Aces-Electronics/ae-temperature-monitor/firmware/src/services/ble_service.cpp

#include "ble_service.h"
#include <Arduino.h>
#include <WiFi.h>

// UUIDs
#define SERVICE_UUID        "4fafc201-1fb5-459e-8fcc-c5c9c331914b" // Reuse Smart Shunt Service for now or defined new
#define TEMP_CHAR_UUID      "beb5483e-36e1-4688-b7f5-ea07361b26a9" // Similar to Voltage but last digit 9
#define SLEEP_CHAR_UUID     "3A1B2C3D-4E5F-6A7B-8C9D-0E1F2A3B4C60" // Reuse disconnect delay or new?
// Actually let's use a specific one for Temp Sensor to distinguish?
// User said: "profiles for the BLE app so that it knows which device is connected"
// I will use a different Service UUID or just different characteristics.
// Let's stick to the Smart Shunt Service UUID for simplicity in discovery but specific characteristics.

#define TEMP_SENSOR_SERVICE_UUID "181A" // Environmental Sensing Service (Standard) or Custom?
// Let's use Custom to match user pattern.
#define AE_TEMP_SERVICE_UUID "4fafc201-1fb5-459e-8fcc-c5c9c331914c" // Ended with 'c'

#define CHAR_TEMP_UUID       "beb5483e-36e1-4688-b7f5-ea07361b26aa"
#define CHAR_SLEEP_UUID      "beb5483e-36e1-4688-b7f5-ea07361b26ab"
#define CHAR_BATT_UUID       "beb5483e-36e1-4688-b7f5-ea07361b26ac"
#define CHAR_NAME_UUID       "beb5483e-36e1-4688-b7f5-ea07361b26ad"
#define CHAR_PAIRED_UUID     "beb5483e-36e1-4688-b7f5-ea07361b26ae"
#define WIFI_SSID_CHAR_UUID  "5A1B2C3D-4E5F-6A7B-8C9D-0E1F2A3B4C62"
#define WIFI_PASS_CHAR_UUID  "6A1B2C3D-4E5F-6A7B-8C9D-0E1F2A3B4C63"

BleService bleService;

class ServerCallbacks: public NimBLEServerCallbacks {
    void onConnect(NimBLEServer* pServer) {
        Serial.println("Client connected");
    };
    void onDisconnect(NimBLEServer* pServer) {
        Serial.println("Client disconnected");
    }
};

class PairedCallback: public NimBLECharacteristicCallbacks {
    void onWrite(NimBLECharacteristic* pCharacteristic) {
        std::string value = pCharacteristic->getValue();
        if (value.length() > 0) {
            String valStr = String(value.c_str());
            Serial.printf("[BLE WRITE] Paired/Reset Command: %s\n", valStr.c_str());
            
            if (valStr.startsWith("{")) {
                // JSON Payload -> Pairing Data
                if (bleService._pairingDataCallback) {
                     bleService._pairingDataCallback(valStr.c_str());
                }
            } else if (valStr == "FORCE_OTA") {
                 Serial.println("[BLE] FORCE_OTA command received.");
                 if (bleService._forceOtaCallback) {
                      bleService._forceOtaCallback();
                 }
            } else if (valStr == "RESET" || valStr == "UNPAIR") {
                // Reset Command
                 Serial.println("Received RESET command");
                 bleService.updatePaired(false);
            } 
        }
    }
};

class WifiSsidCallback: public NimBLECharacteristicCallbacks {
    void onWrite(NimBLECharacteristic* pCharacteristic) {
        std::string value = pCharacteristic->getValue();
        if (value.length() > 0) {
             bleService._tempSsid = String(value.c_str());
             Serial.printf("[BLE WRITE] WiFi SSID: %s\n", bleService._tempSsid.c_str());
             // Pass partial or full data. If Pass is already set, this might be a refresh.
             if (bleService._wifiCallback) {
                  bleService._wifiCallback(bleService._tempSsid.c_str(), bleService._tempPass.c_str());
             }
        }
    }
};

class WifiPassCallback: public NimBLECharacteristicCallbacks {
    void onWrite(NimBLECharacteristic* pCharacteristic) {
        std::string value = pCharacteristic->getValue();
        if (value.length() > 0) {
             bleService._tempPass = String(value.c_str());
             Serial.println("[BLE WRITE] WiFi Pass received");
             if (bleService._wifiCallback) {
                  bleService._wifiCallback(bleService._tempSsid.c_str(), bleService._tempPass.c_str());
             }
        }
    }
};

class SleepCallback: public NimBLECharacteristicCallbacks {
    void onWrite(NimBLECharacteristic* pCharacteristic) {
        std::string value = pCharacteristic->getValue();
        if (value.length() == 4) {
             uint32_t interval = *(uint32_t*)value.data();
             bleService.setSleepInterval(interval);
             Serial.printf("[BLE WRITE] Sleep Interval: %d ms\n", interval);
        }
    }
};

class NameCallback: public NimBLECharacteristicCallbacks {
    void onWrite(NimBLECharacteristic* pCharacteristic) {
        std::string value = pCharacteristic->getValue();
        if (value.length() > 0) {
             Serial.printf("[BLE WRITE] Device Name: %s\n", value.c_str());
             bleService.updateName(value.c_str()); // Helper to notify listener
        }
    }
};


// Helper to generate PIN from MAC (Matches Shunt)
uint32_t generatePinFromMac() {
    uint8_t mac[6];
    WiFi.macAddress(mac);
    // Use last 3 bytes to generate a unique 6-digit PIN
    uint32_t val = (mac[3] << 16) | (mac[4] << 8) | mac[5];
    uint32_t pin = val % 1000000;
    Serial.printf("[BLE SEC] PIN Code: %06d\n", pin);
    return pin;
}

void BleService::begin(const char* deviceName) {
    NimBLEDevice::init(deviceName);
    NimBLEDevice::setPower(ESP_PWR_LVL_P9);
    
    // Security & Speed Configuration (Matches Shunt)
    uint32_t passkey = generatePinFromMac();
    NimBLEDevice::setSecurityAuth(true, true, true); // Bonding, MITM, Secure Connection
    NimBLEDevice::setSecurityPasskey(passkey);
    NimBLEDevice::setSecurityIOCap(BLE_HS_IO_DISPLAY_ONLY); // Forces user to enter PIN on phone
    
    _pServer = NimBLEDevice::createServer();
    _pServer->setCallbacks(new ServerCallbacks());
    
    _pService = _pServer->createService(AE_TEMP_SERVICE_UUID);
    
    _pTempChar = _pService->createCharacteristic(
        CHAR_TEMP_UUID,
        NIMBLE_PROPERTY::READ | NIMBLE_PROPERTY::NOTIFY | NIMBLE_PROPERTY::READ_ENC
    );
    
    _pSleepChar = _pService->createCharacteristic(
        CHAR_SLEEP_UUID,
        NIMBLE_PROPERTY::READ | NIMBLE_PROPERTY::WRITE | NIMBLE_PROPERTY::READ_ENC | NIMBLE_PROPERTY::WRITE_ENC
    );
    _pSleepChar->setCallbacks(new SleepCallback());
    _pSleepChar->setValue((uint8_t*)&_sleepIntervalMs, 4);
    
    _pBattChar = _pService->createCharacteristic(
        CHAR_BATT_UUID,
        NIMBLE_PROPERTY::READ | NIMBLE_PROPERTY::NOTIFY | NIMBLE_PROPERTY::READ_ENC
    );
    
    
    _pNameChar = _pService->createCharacteristic(
        CHAR_NAME_UUID,
        NIMBLE_PROPERTY::READ | NIMBLE_PROPERTY::WRITE | NIMBLE_PROPERTY::NOTIFY | NIMBLE_PROPERTY::READ_ENC | NIMBLE_PROPERTY::WRITE_ENC
    );
    _pNameChar->setCallbacks(new NameCallback());
    _pNameChar->setValue(deviceName);

    // PAIRED Characteristic
    _pPairedChar = _pService->createCharacteristic(
        CHAR_PAIRED_UUID,
        NIMBLE_PROPERTY::READ | NIMBLE_PROPERTY::WRITE | NIMBLE_PROPERTY::NOTIFY | NIMBLE_PROPERTY::READ_ENC | NIMBLE_PROPERTY::WRITE_ENC
    );
    // Set initial value to WiFi MAC Address
    String mac = WiFi.macAddress();
    _pPairedChar->setValue(mac.c_str());
    _pPairedChar->setCallbacks(new PairedCallback());

    // WIFI Credentials
    _pWifiSsidChar = _pService->createCharacteristic(
        WIFI_SSID_CHAR_UUID,
         NIMBLE_PROPERTY::WRITE | NIMBLE_PROPERTY::WRITE_ENC
    );
    _pWifiSsidChar->setCallbacks(new WifiSsidCallback());
    
    _pWifiPassChar = _pService->createCharacteristic(
        WIFI_PASS_CHAR_UUID,
         NIMBLE_PROPERTY::WRITE | NIMBLE_PROPERTY::WRITE_ENC
    );
    _pWifiPassChar->setCallbacks(new WifiPassCallback());

    // Start Service
    _pService->start();

    // Start Advertising
    NimBLEAdvertising* pAdvertising = NimBLEDevice::getAdvertising();
    pAdvertising->addServiceUUID(AE_TEMP_SERVICE_UUID); // Advertise Service UUID
    // Explicitly add Name to Scan Response to handle long suffixes
    NimBLEAdvertisementData oScanResponseData = NimBLEAdvertisementData();
    oScanResponseData.setName(deviceName);
    pAdvertising->setScanResponseData(oScanResponseData);
    
    pAdvertising->setScanResponse(true);
    pAdvertising->start();
    
    Serial.println("BLE Started (Secure)");
}

void BleService::updateTemperature(float temp) {
    if (_pTempChar) {
        _pTempChar->setValue(temp);
        _pTempChar->notify();
    }
}

void BleService::updateBatteryLevel(int level) {
    if (_pBattChar) {
        _pBattChar->setValue((uint32_t)level); // Simplification
        _pBattChar->notify();
    }
}

void BleService::updateName(const char* name) {
    if (_pNameChar) {
        // Explicitly construct string to ensure deep copy and length calculation
        std::string n(name);
        Serial.printf("DEBUG: BLE updating name char to: '%s' (len %d)\n", n.c_str(), n.length());
        _pNameChar->setValue(n);
        _pNameChar->notify();
    }
    if (_nameCallback) {
        _nameCallback(name);
    }
}

void BleService::updatePaired(bool paired) {
    _isPaired = paired;
    if (_pPairedChar) {
        uint8_t val = paired ? 1 : 0;
        _pPairedChar->setValue(&val, 1);
        _pPairedChar->notify();
    }
    if (_pairedCallback) {
        _pairedCallback(paired);
    }
}

void BleService::setNameCallback(std::function<void(const char*)> cb) {
    _nameCallback = cb;
}

void BleService::setPairedCallback(std::function<void(bool)> cb) {
    _pairedCallback = cb;
}

void BleService::setPairingDataCallback(std::function<void(const char*)> cb) {
    _pairingDataCallback = cb;
}

void BleService::setWifiCallback(std::function<void(const char*, const char*)> cb) {
    _wifiCallback = cb;
}

void BleService::setForceOtaCallback(std::function<void()> cb) {
    _forceOtaCallback = cb;
}

uint32_t BleService::getSleepInterval() {
    return _sleepIntervalMs;
}

void BleService::setSleepInterval(uint32_t interval) {
    _sleepIntervalMs = interval;
}

bool BleService::isConnected() {
    return _pServer->getConnectedCount() > 0;
}

bool BleService::isPaired() {
    return _isPaired;
}

void BleService::setPaired(bool paired) {
    _isPaired = paired;
}

void BleService::startAdvertising() {
    NimBLEAdvertising* pAdvertising = NimBLEDevice::getAdvertising();
    if (pAdvertising) {
        pAdvertising->start();
        Serial.println("[BLE] Advertising Restarted");
    }
}
