Aces-Electronics/ae-temperature-monitor/firmware/src/services/ble_service.h

#ifndef BLE_SERVICE_H
#define BLE_SERVICE_H

#include <NimBLEDevice.h>

class BleService {
    friend class PairedCallback;
    friend class WifiSsidCallback;
    friend class WifiPassCallback;
    friend class SleepCallback;
    friend class NameCallback;
    
public:
    void begin(const char* deviceName);
    void updateTemperature(float temp);
    void updateBatteryLevel(int level);
    void updateName(const char* name);
    uint32_t getSleepInterval();
    bool isConnected();
    void setSleepInterval(uint32_t interval);
    void setNameCallback(std::function<void(const char*)> cb);
    void setPairedCallback(std::function<void(bool)> cb);
    void updatePaired(bool paired);
    bool isPaired();
    void setPaired(bool paired);
    void setPairingDataCallback(std::function<void(const char*)> cb);
    void setWifiCallback(std::function<void(const char*, const char*)> cb);
    void setForceOtaCallback(std::function<void()> cb);
    void startAdvertising();
    
    // Make callback accessible to friend class or just public helper
    std::function<void(const char*)> _pairingDataCallback;

private:
    static void onConnect(NimBLEServer* pServer);
    static void onDisconnect(NimBLEServer* pServer);
    
    NimBLEServer* _pServer;
    NimBLEService* _pService;
    NimBLECharacteristic* _pTempChar;
    NimBLECharacteristic* _pSleepChar;
    NimBLECharacteristic* _pBattChar;
    NimBLECharacteristic* _pNameChar;
    NimBLECharacteristic* _pPairedChar;
    NimBLECharacteristic* _pWifiSsidChar;
    NimBLECharacteristic* _pWifiPassChar;
    
    std::function<void(const char*)> _nameCallback;
    std::function<void(bool)> _pairedCallback;
    std::function<void(const char*, const char*)> _wifiCallback;
    std::function<void()> _forceOtaCallback;
    
    bool _deviceConnected = false;
    uint32_t _sleepIntervalMs = 900000; // Default 15 mins
    bool _isPaired = false;
    
    // Temp storage for WiFi creds until both are received or processed
    String _tempSsid;
    String _tempPass;
};

extern BleService bleService;

#endif // BLE_SERVICE_H
