Aces-Electronics/ae-temperature-monitor/firmware/src/services/espnow_service.h

#ifndef ESPNOW_SERVICE_H
#define ESPNOW_SERVICE_H

#include <Arduino.h>
#include <esp_now.h>
#include <WiFi.h>
#include "shared_defs.h"

typedef struct_message_temp_sensor TempSensorData;

class EspNowService {
public:
    void begin();
    void registerRecvCallback(esp_now_recv_cb_t callback);
    void broadcast(const TempSensorData& data);
    void sendToPeer(const TempSensorData& data, const uint8_t* peerMac);
    void addSecurePeer(const char* macStr, const char* keyStr);
    
    void setForceBroadcast(bool force) { m_forceBroadcast = force; }
    bool isForceBroadcast() { return m_forceBroadcast; }
    
    volatile bool sendFinished = false;
    volatile bool sendSuccess = false;
    void resetSendStatus() { sendFinished = false; sendSuccess = false; }

private:
    static void onDataSent(const uint8_t *mac_addr, esp_now_send_status_t status);
    bool m_forceBroadcast = false;
};

extern EspNowService espNowService;

#endif // ESPNOW_SERVICE_H
